DhairyaAPImaster/The-cycle-Smartener/images/image (3).webp

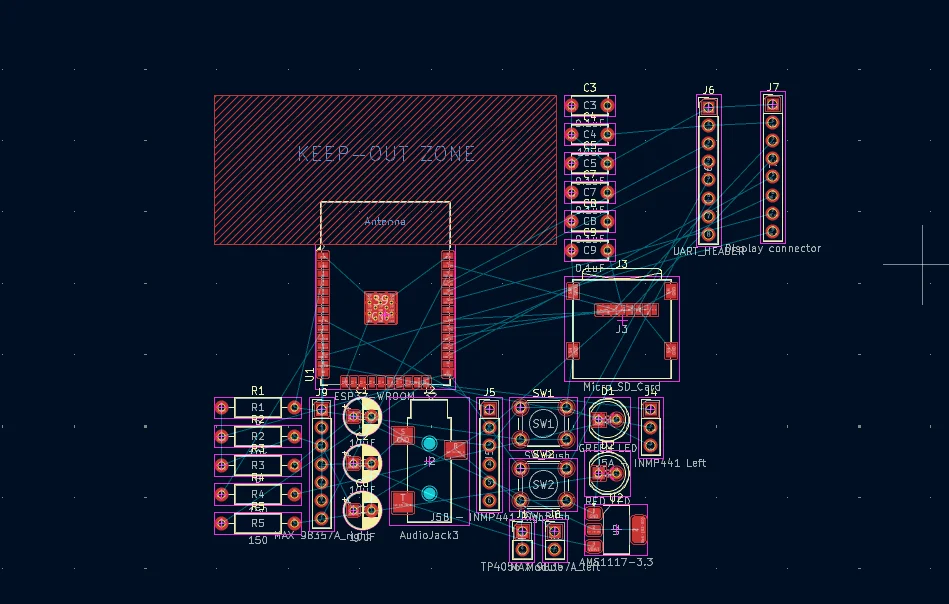
images/image (3).webp
