DhairyaAPImaster/The-cycle-Smartener/images/image (4).webp

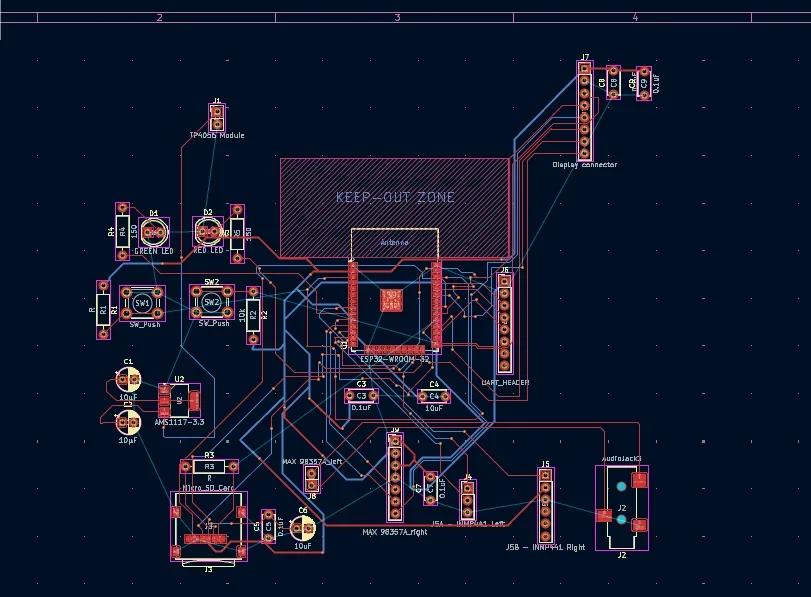
images/image (4).webp
