DhairyaAPImaster/The-cycle-Smartener/images/image (1).png

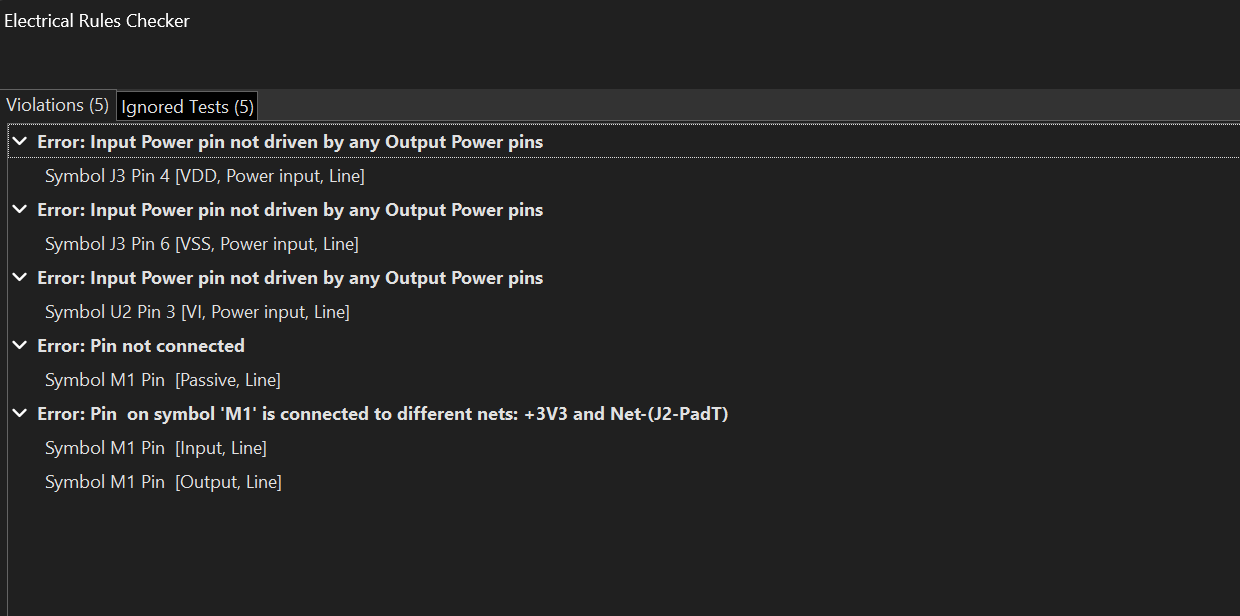
images/image (1).png
