DhairyaAPImaster/The-cycle-Smartener/images/image (1).webp

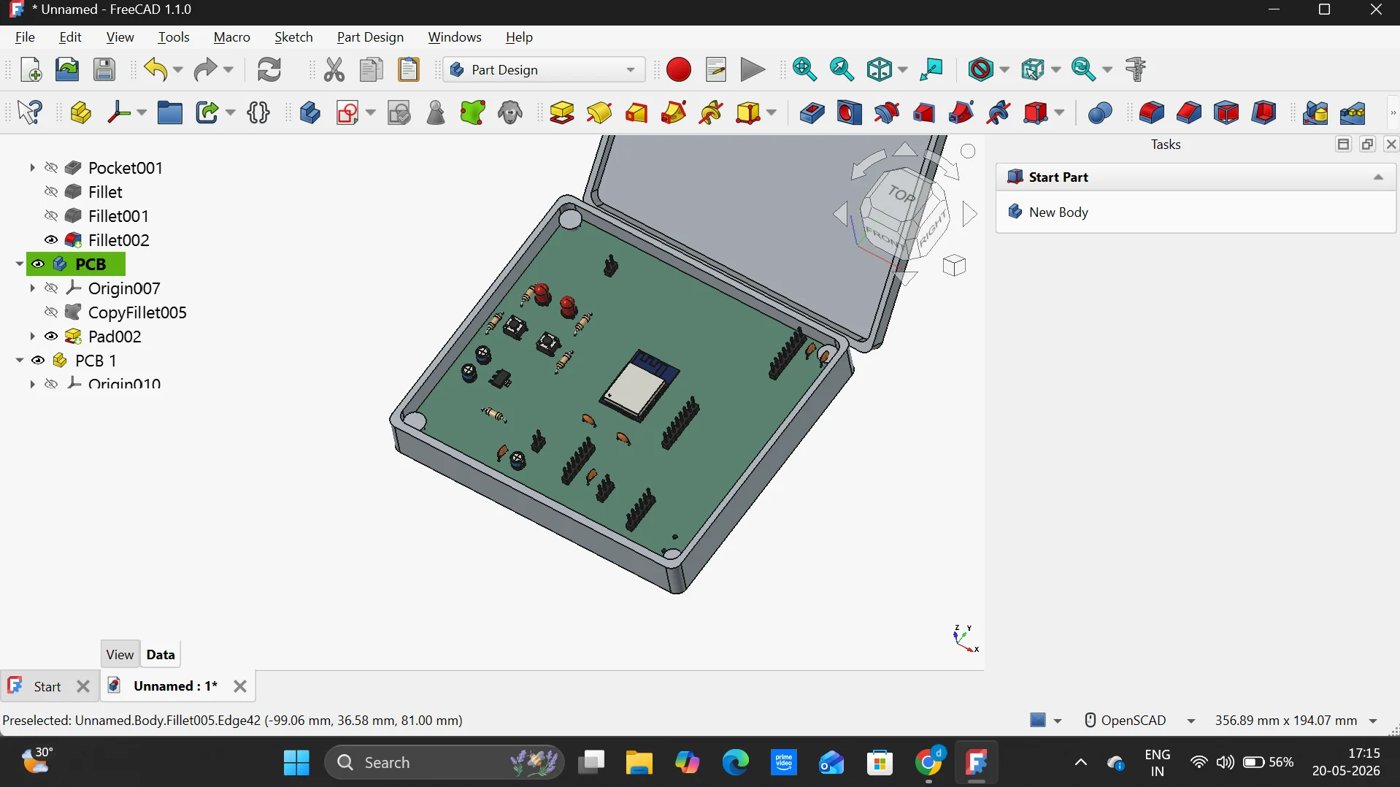
images/image (1).webp
