DhairyaAPImaster/The-cycle-Smartener/images/image (2).png

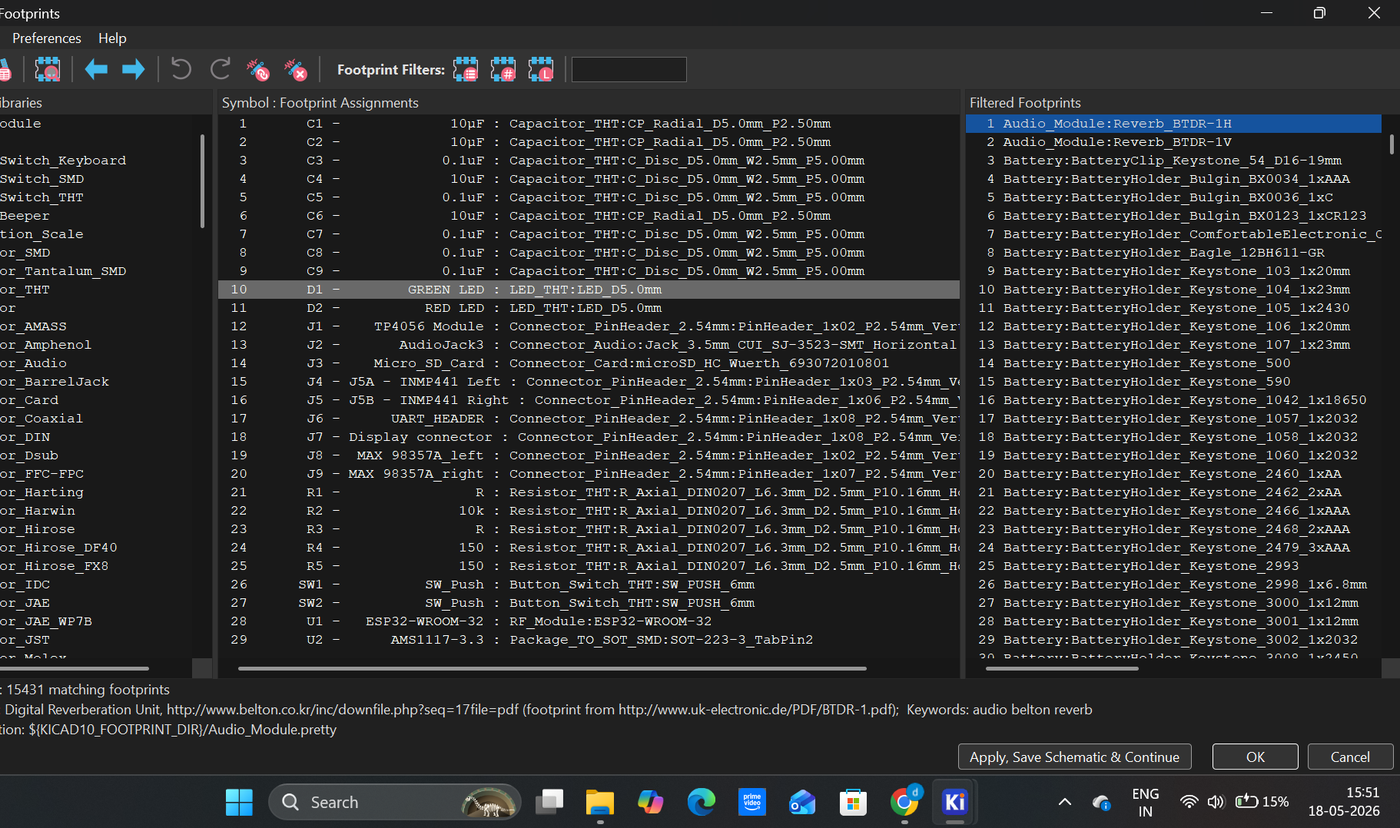
images/image (2).png
