DhairyaAPImaster/The-cycle-Smartener/images/image (2).webp

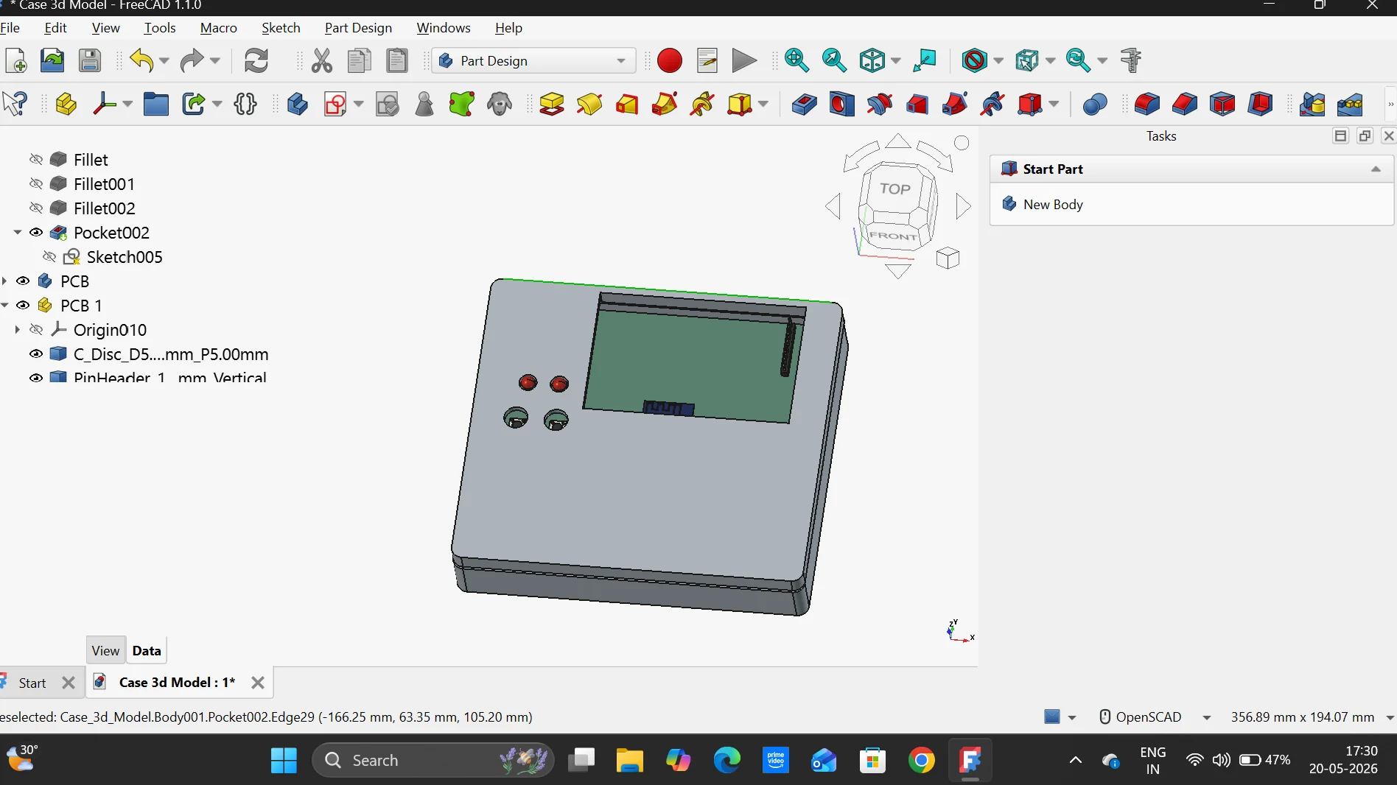
images/image (2).webp
