DhairyaAPImaster/The-cycle-Smartener/images/image (3).png

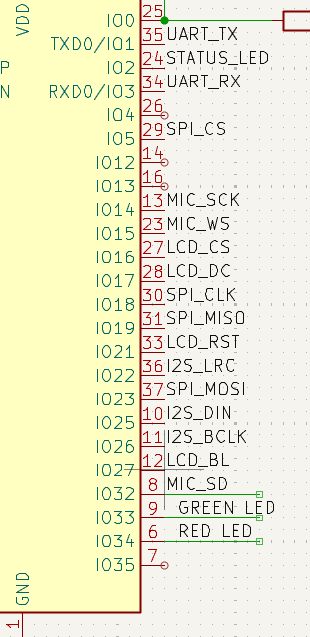
images/image (3).png
