DhairyaAPImaster/The-cycle-Smartener/images/image (4).png

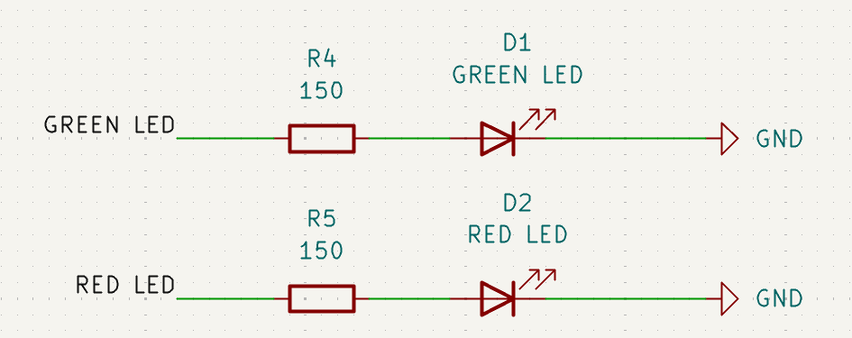
images/image (4).png
