DhairyaAPImaster/The-cycle-Smartener/images/image (5).png

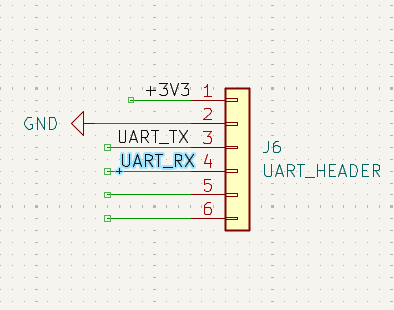
images/image (5).png
