DhairyaAPImaster/The-cycle-Smartener/images/image (5).webp

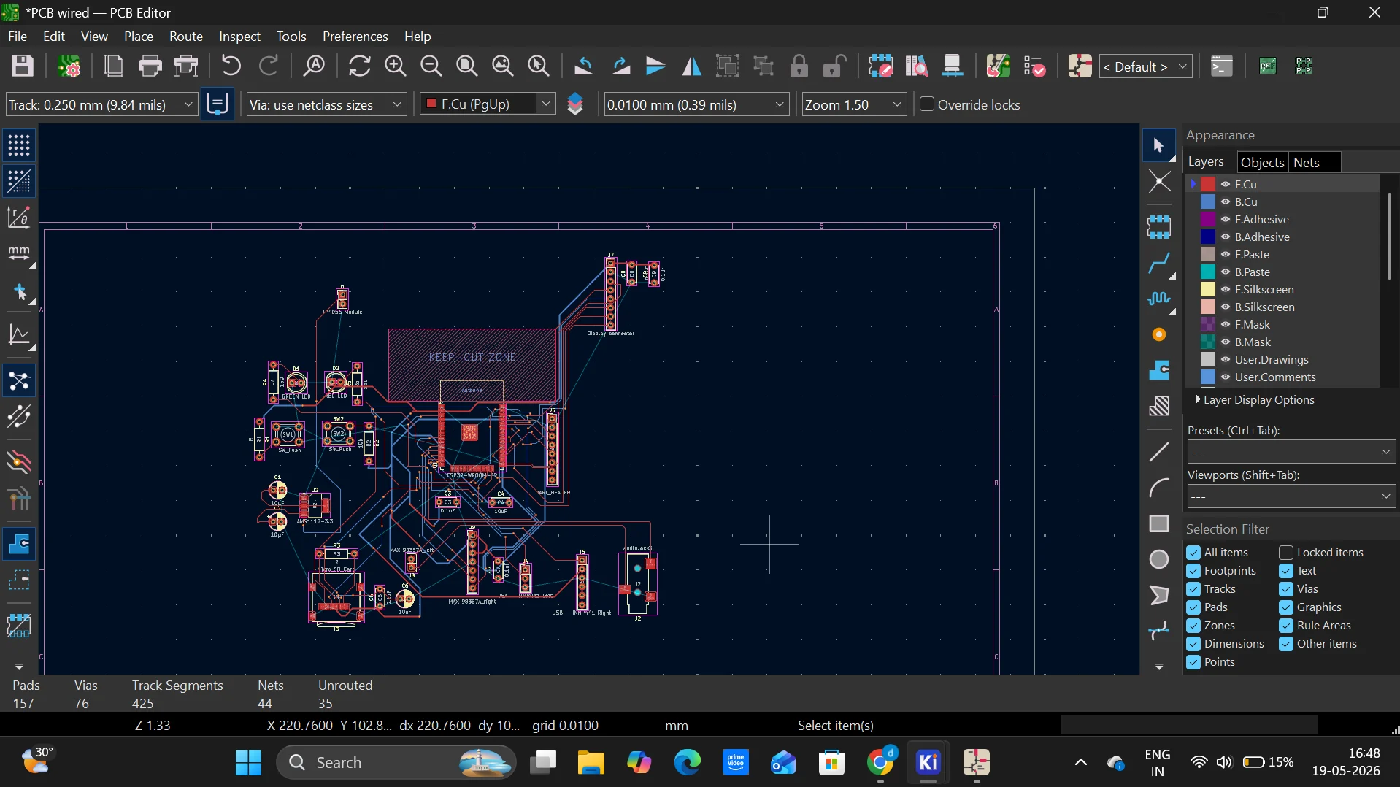
images/image (5).webp
