DhairyaAPImaster/The-cycle-Smartener/images/image (6).png

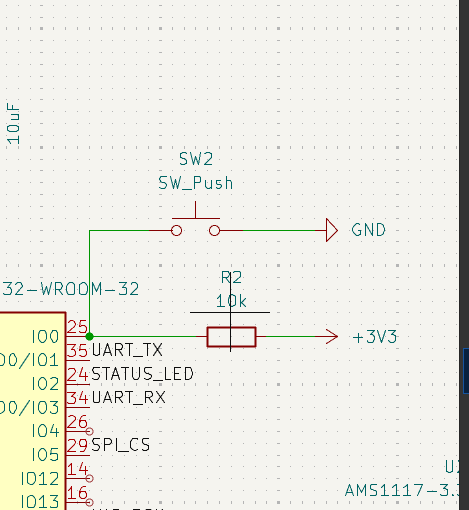
images/image (6).png
