DhairyaAPImaster/The-cycle-Smartener/images/image (6).webp

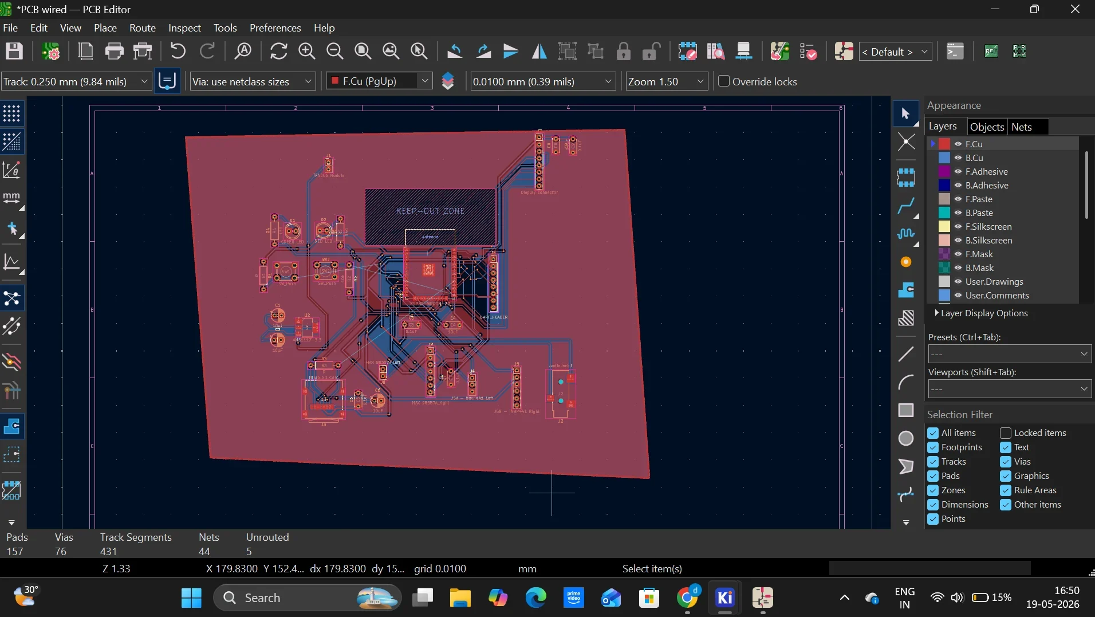
images/image (6).webp
