DhairyaAPImaster/The-cycle-Smartener/images/image (7).png

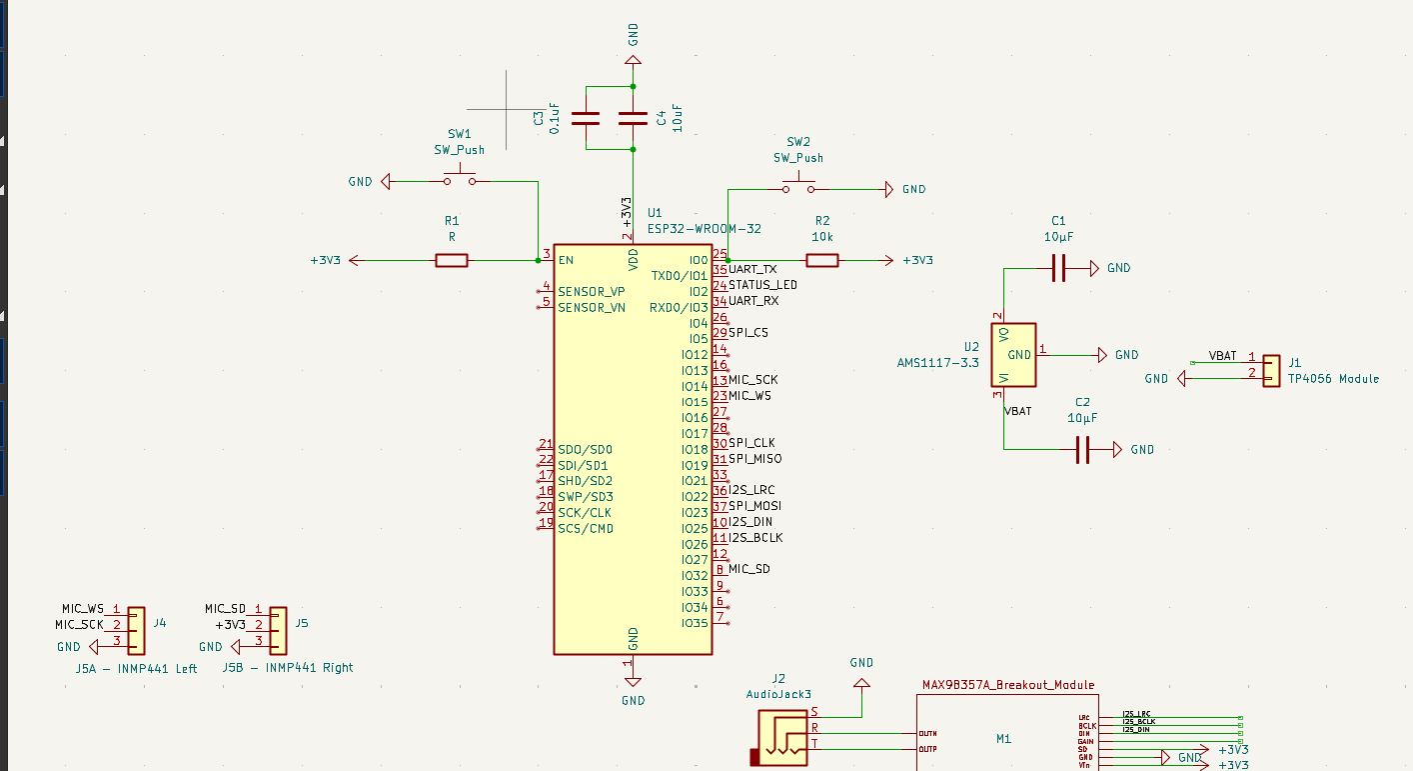
images/image (7).png
