DhairyaAPImaster/The-cycle-Smartener/images/image (7).webp

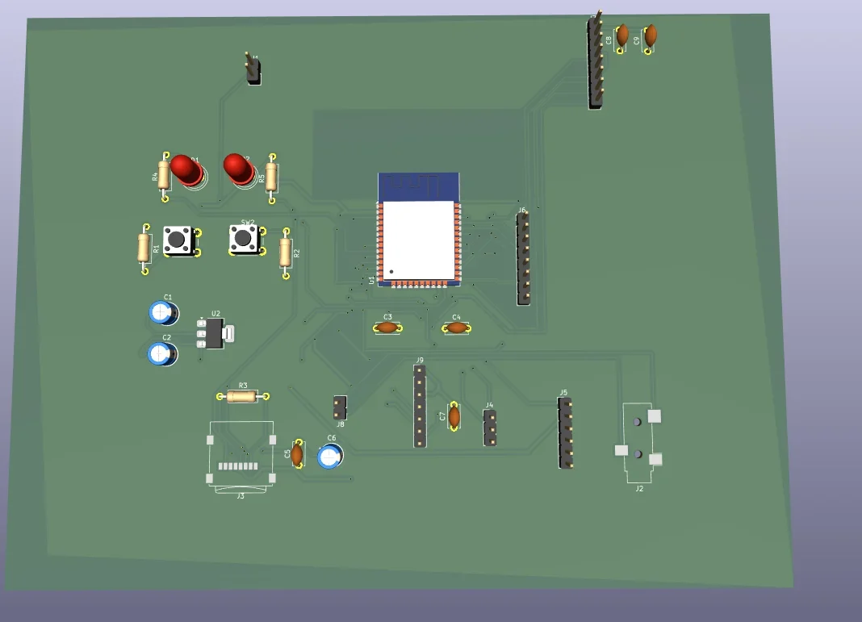
images/image (7).webp
