DhairyaAPImaster/The-cycle-Smartener/images/image (8).png

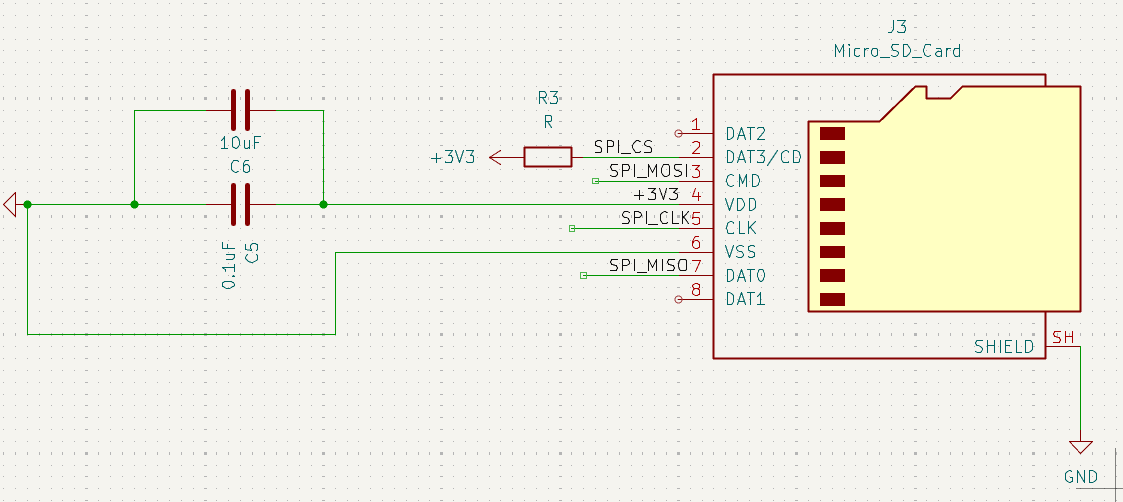
images/image (8).png
