DhairyaAPImaster/The-cycle-Smartener/images/image (8).webp

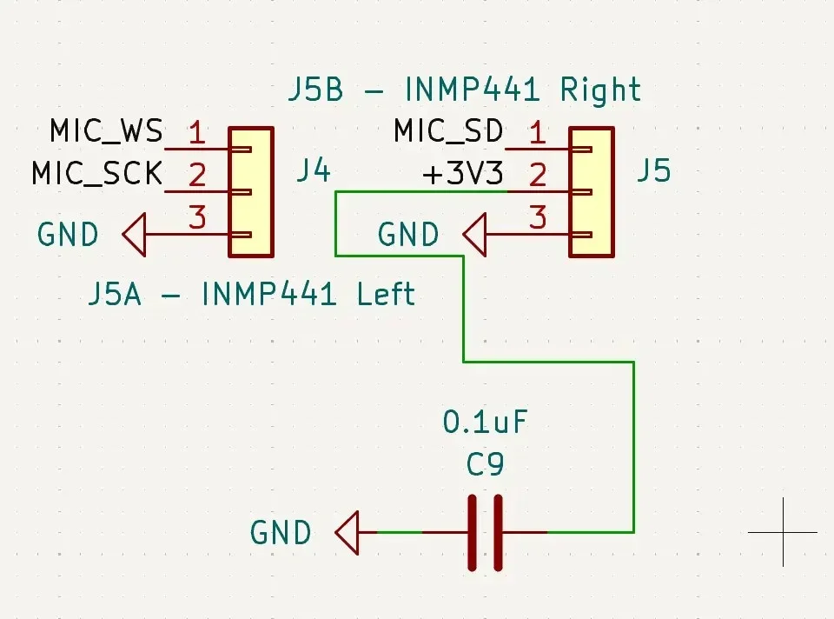
images/image (8).webp
