DhairyaAPImaster/The-cycle-Smartener/images/image (9).png

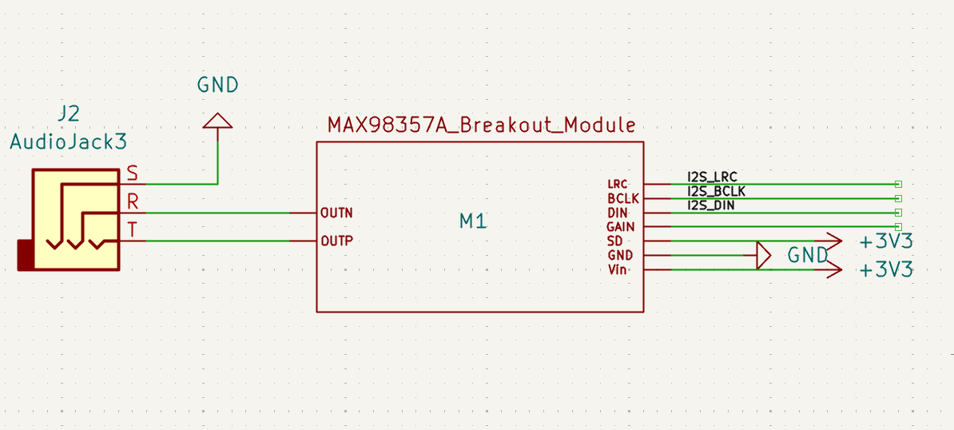
images/image (9).png
