DhairyaAPImaster/The-cycle-Smartener/images/image (9).webp

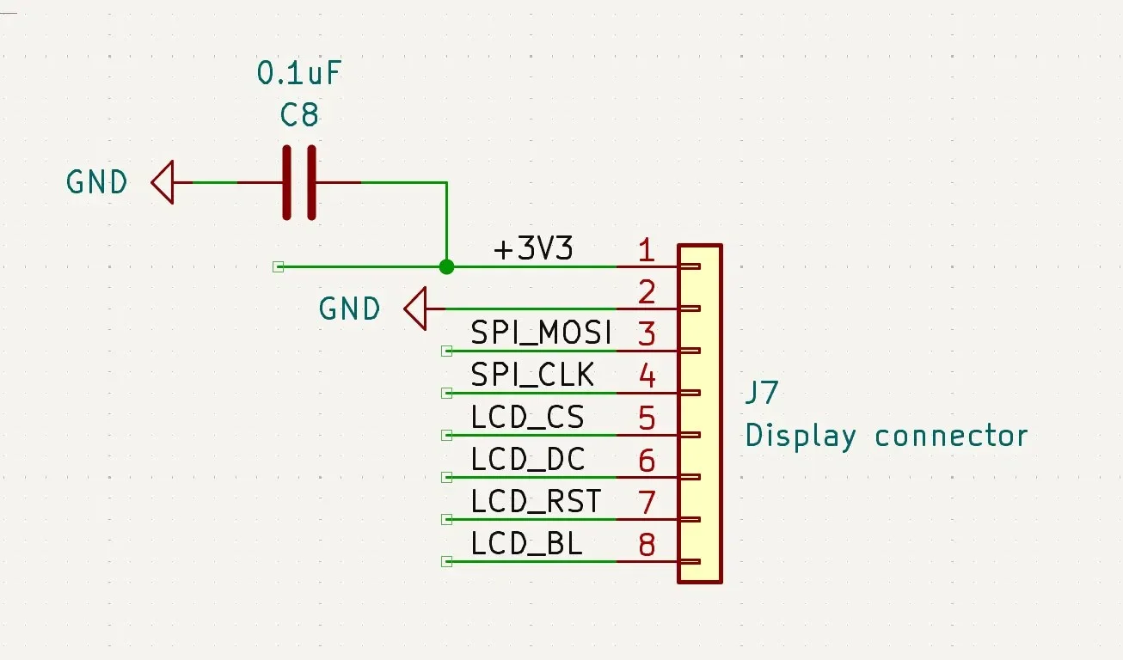
images/image (9).webp
