DhairyaAPImaster/The-cycle-Smartener/images/image (10).png

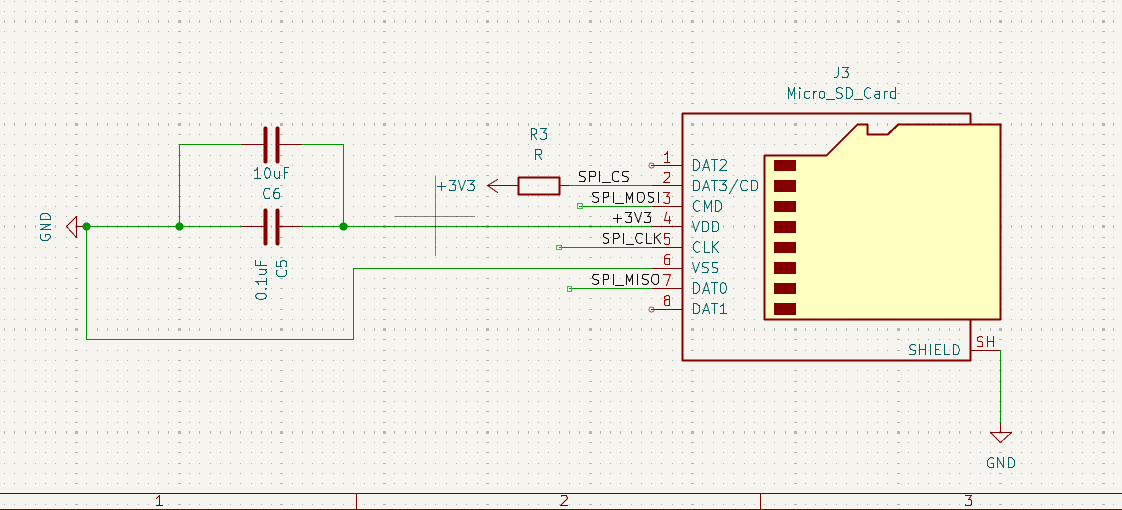
images/image (10).png
