DhairyaAPImaster/The-cycle-Smartener/images/image (10).webp

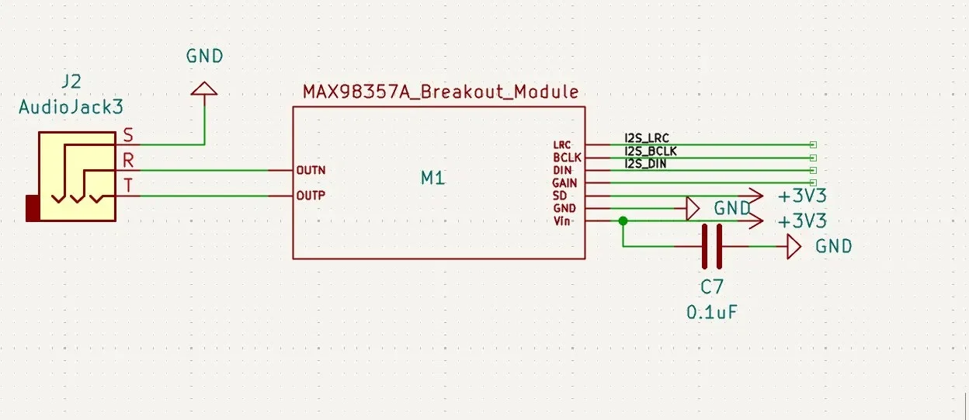
images/image (10).webp
