DhairyaAPImaster/The-cycle-Smartener/images/image (11).png

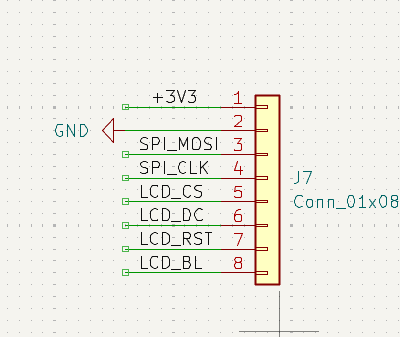
images/image (11).png
