DhairyaAPImaster/The-cycle-Smartener/images/image (11).webp

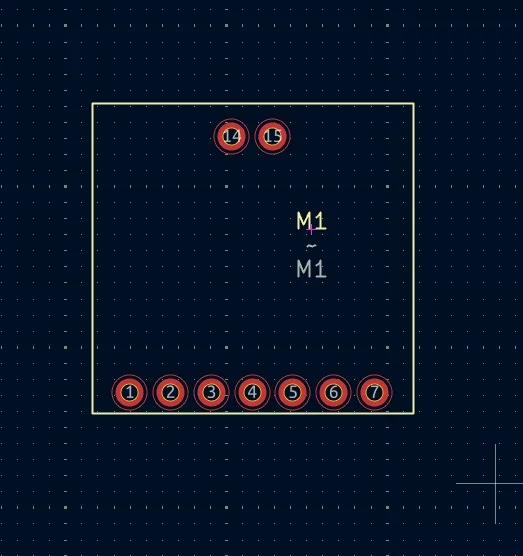
images/image (11).webp
