DhairyaAPImaster/The-cycle-Smartener/images/image (12).webp

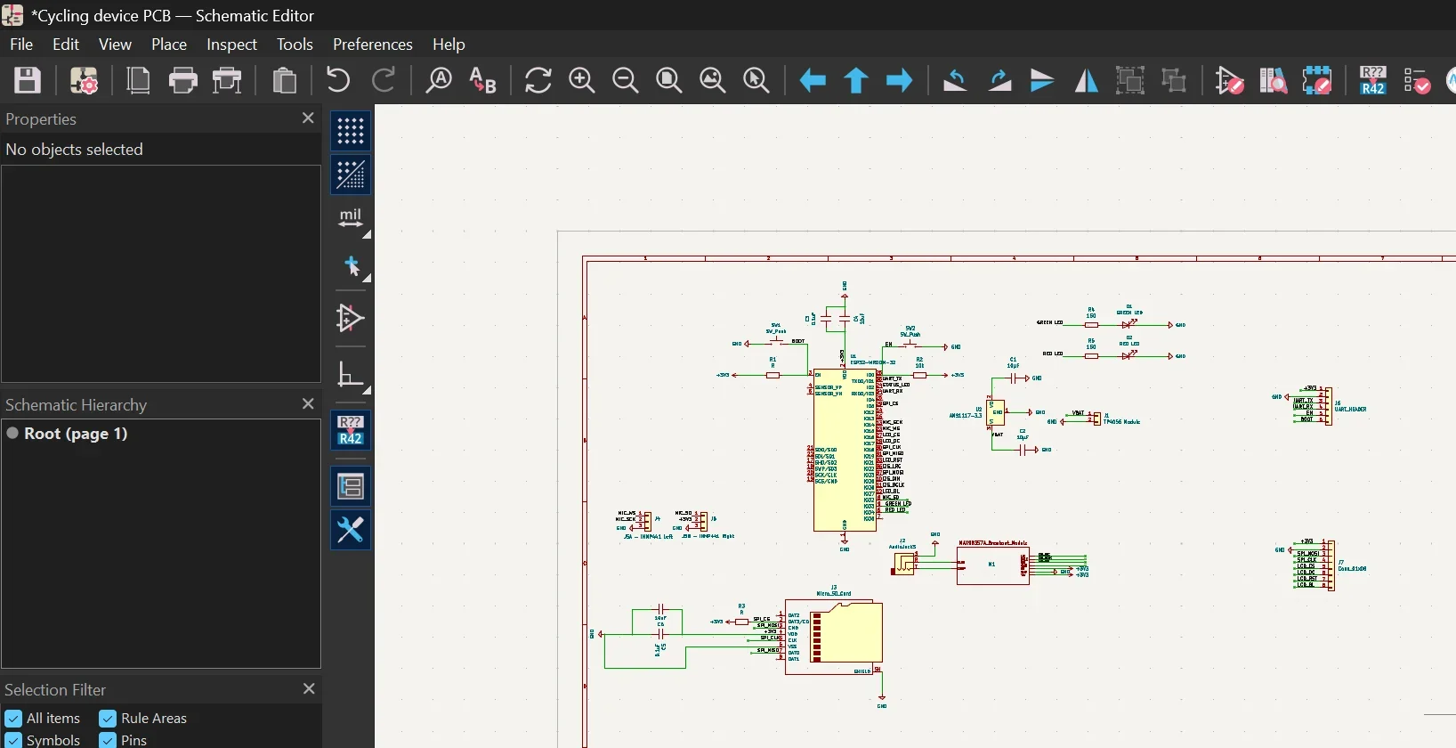
images/image (12).webp
