DhairyaAPImaster/The-cycle-Smartener/images/image (13).webp

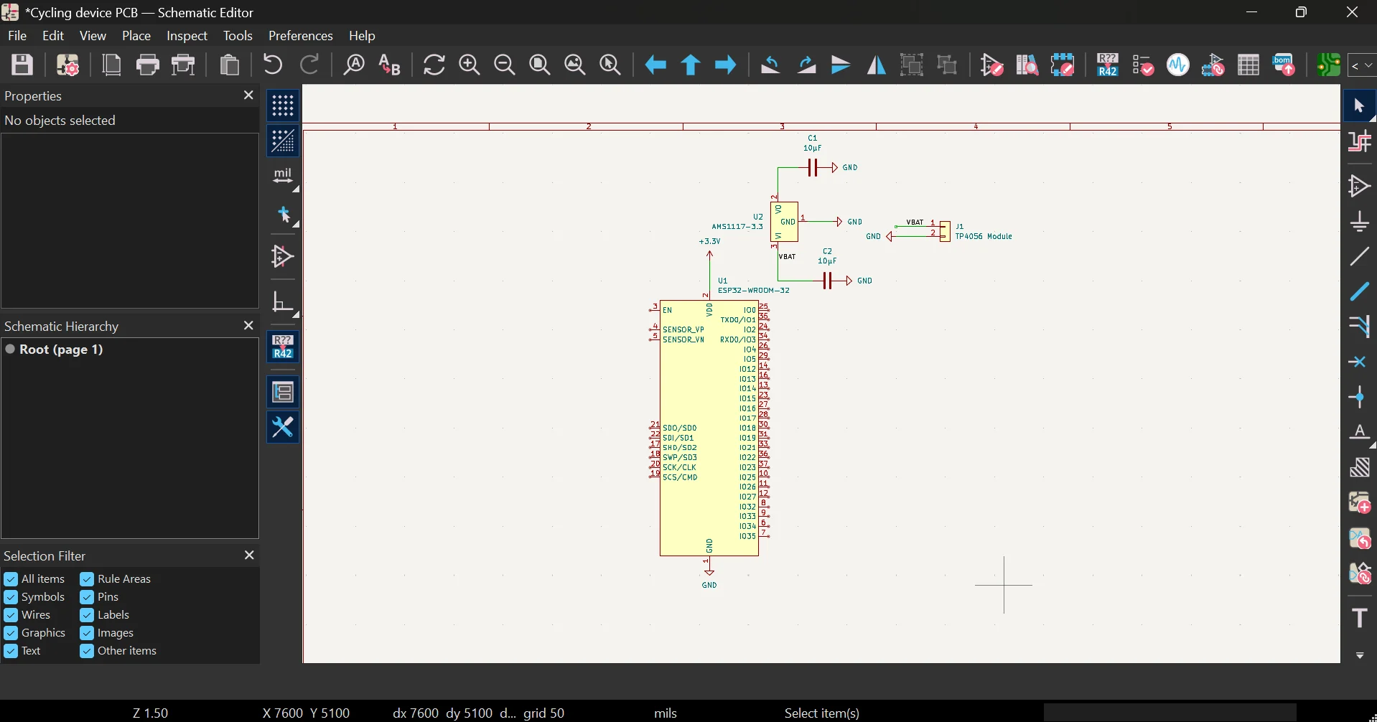
images/image (13).webp
