DhairyaAPImaster/The-cycle-Smartener/images/image.png

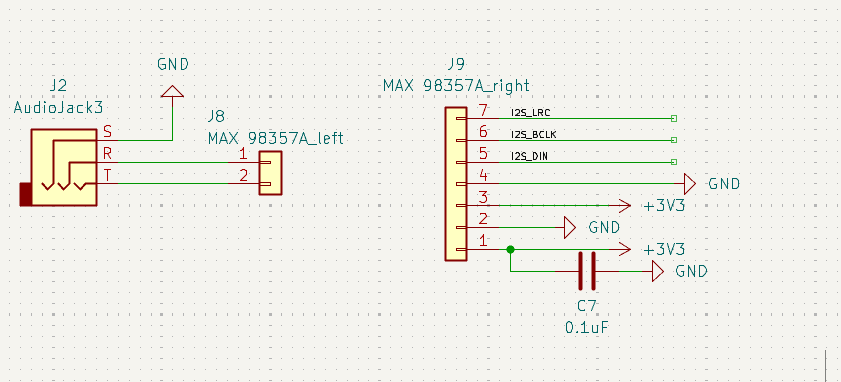
images/image.png
