DhairyaAPImaster/The-cycle-Smartener/images/Screenshot 2026-06-17 182830.png

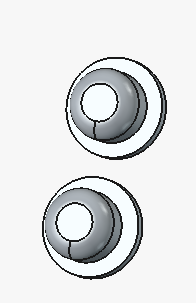
images/Screenshot 2026-06-17 182830.png
