DhairyaAPImaster/The-cycle-Smartener/images/Screenshot 2026-06-17 182845.png

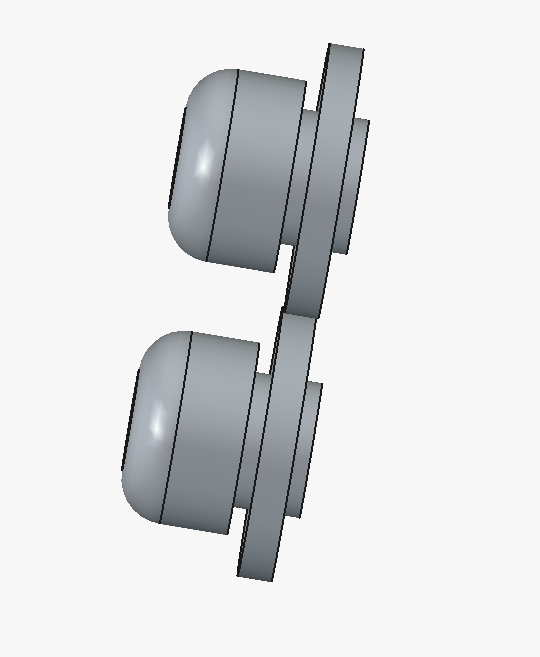
images/Screenshot 2026-06-17 182845.png
