DhairyaAPImaster/The-cycle-Smartener/images/Screenshot 2026-06-17 182929.png

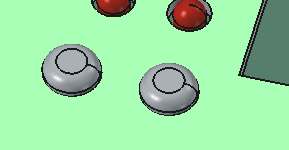
images/Screenshot 2026-06-17 182929.png
