DhairyaAPImaster/The-cycle-Smartener/images/Screenshot 2026-06-17 185231.png

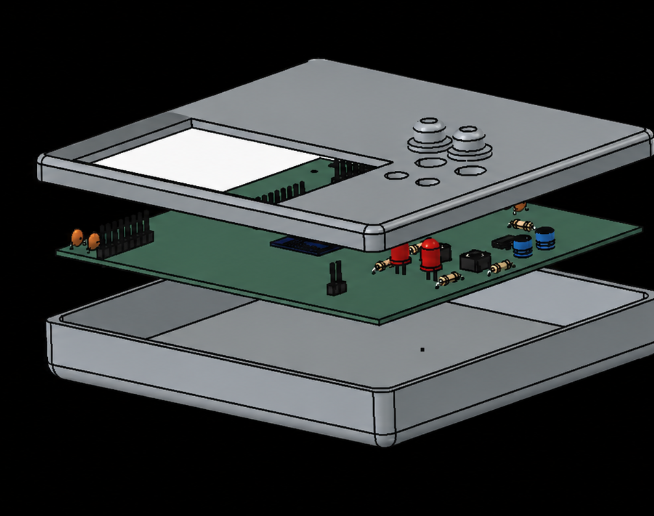
images/Screenshot 2026-06-17 185231.png
